warthog9/ABQMMF-Solderkit-2018/src/boot.py

# This file is executed on every boot (including wake-boot from deepsleep)
#import esp
#esp.osdebug(None)
import gc
#import webrepl
#webrepl.start()
gc.collect()

import network
sta_if = network.WLAN(network.STA_IF)
ap_if =  network.WLAN(network.AP_IF)

sta_if.active(False)
ap_if.active(False)
